smartboxchannel/EFEKTA_Pixel_Open_Air_v1_v2/Images/002.png

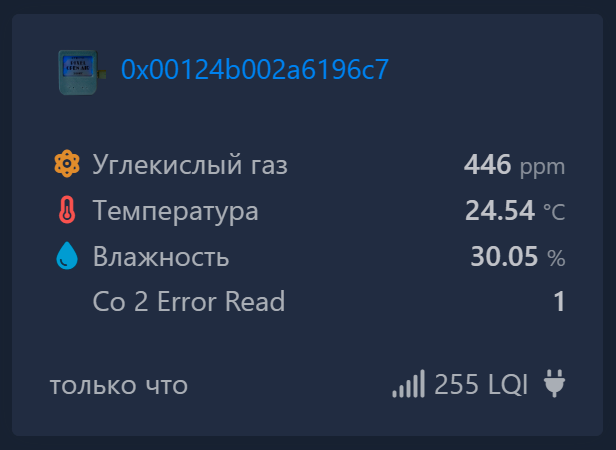
Images/002.png
