smartboxchannel/EFEKTA_Pixel_Open_Air_v1_v2/Images/007.png

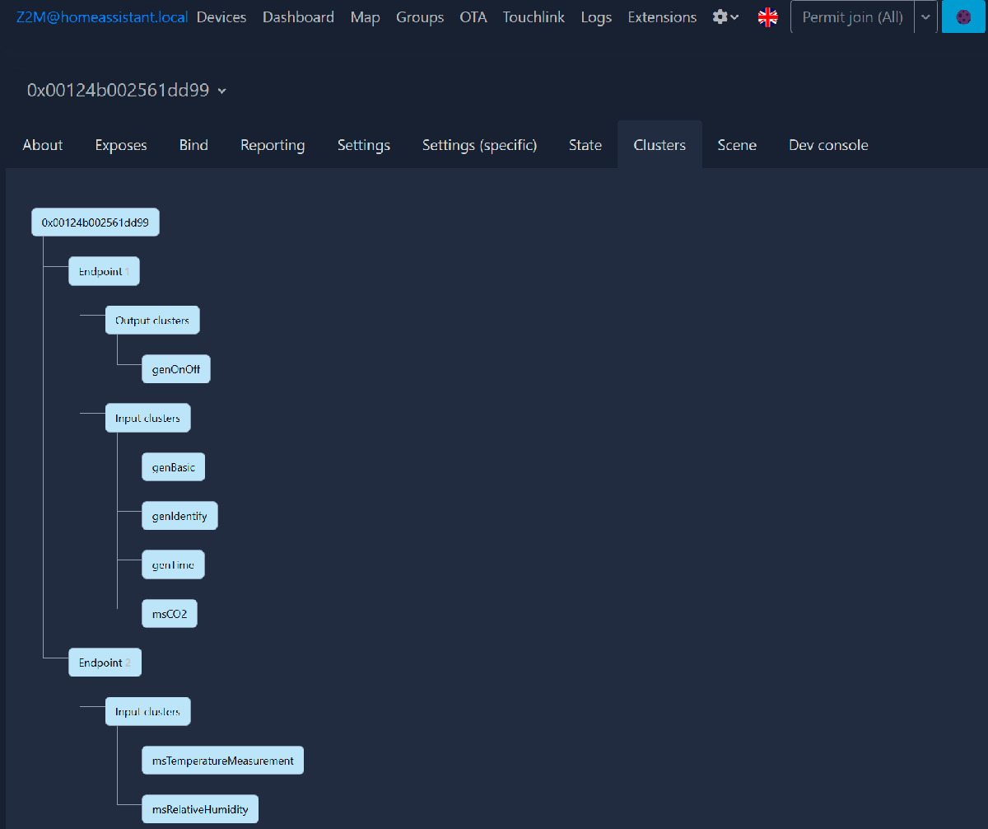
Images/007.png
